kenken64/iot-door-sensor/docs/Annotation 2019-03-16 024516.png

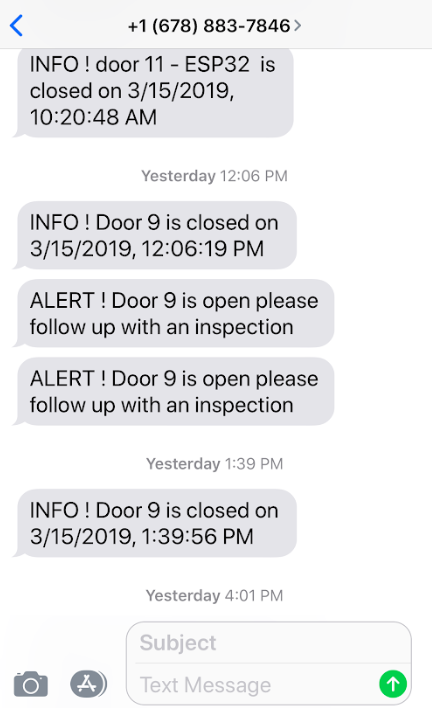
docs/Annotation 2019-03-16 024516.png
