kenken64/iot-door-sensor/docs/arduino_9.jpg

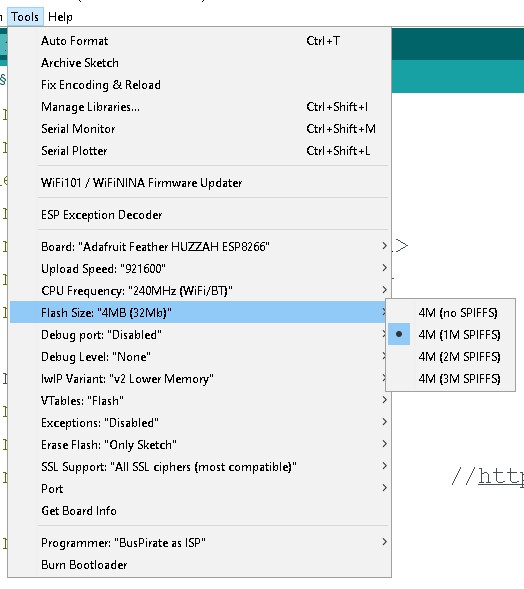
docs/arduino_9.jpg
