kenken64/iot-door-sensor/docs/blynk4.png

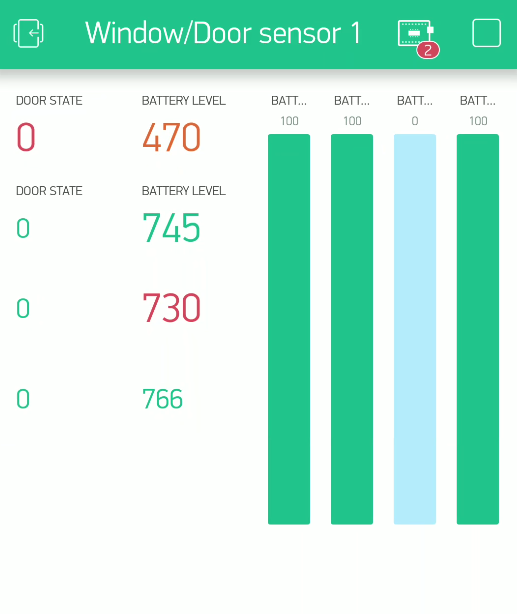
docs/blynk4.png
