kenken64/iot-door-sensor/docs/choose_date_action_was_taken.png

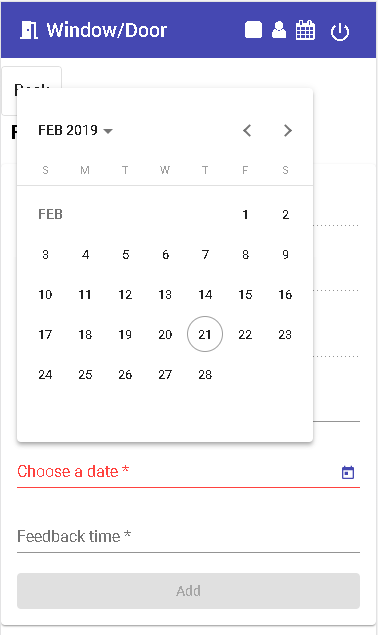
docs/choose_date_action_was_taken.png
