kenken64/iot-door-sensor/docs/door_sensor_wifi.jpg

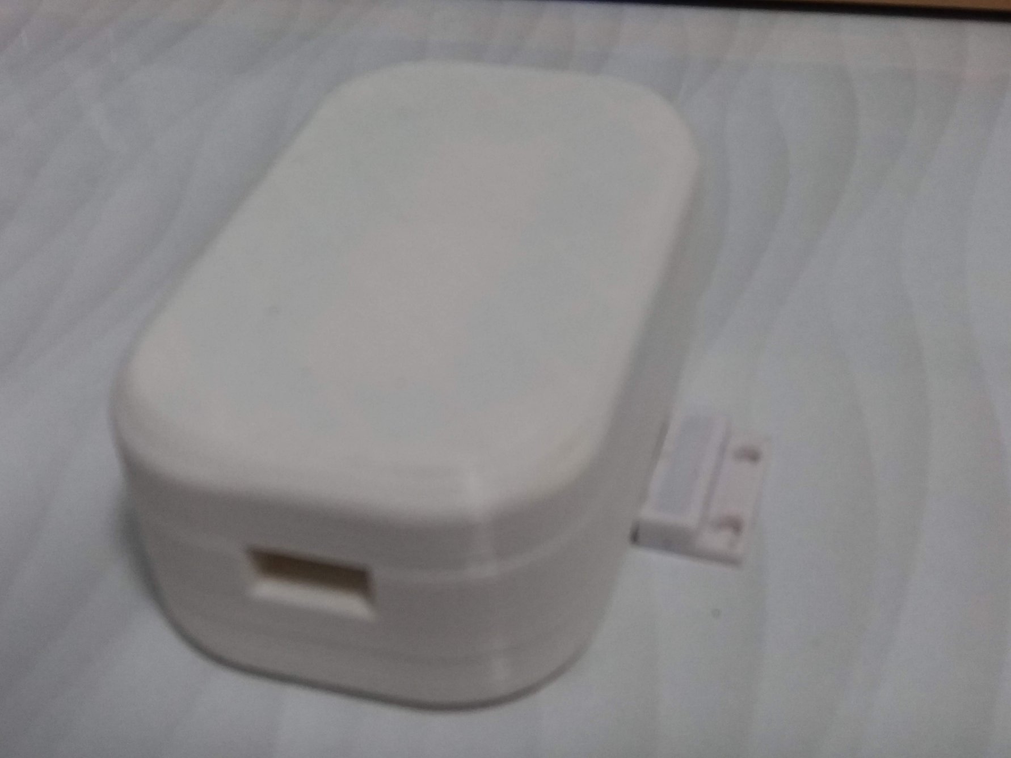
docs/door_sensor_wifi.jpg
