kenken64/iot-door-sensor/docs/filter_feedback.png

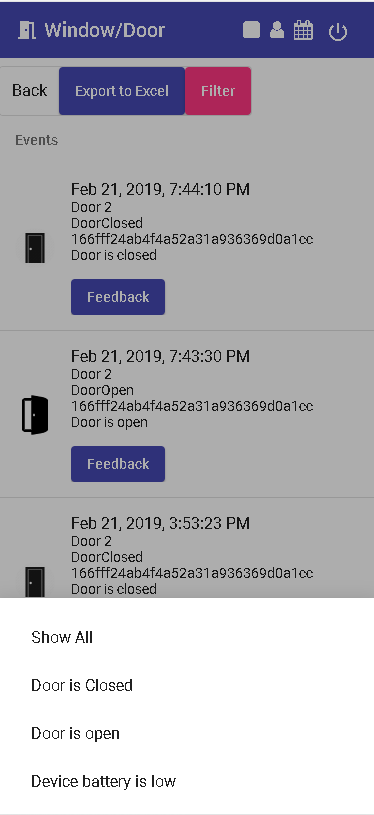
docs/filter_feedback.png
