kenken64/iot-door-sensor/docs/full_in_battery.png

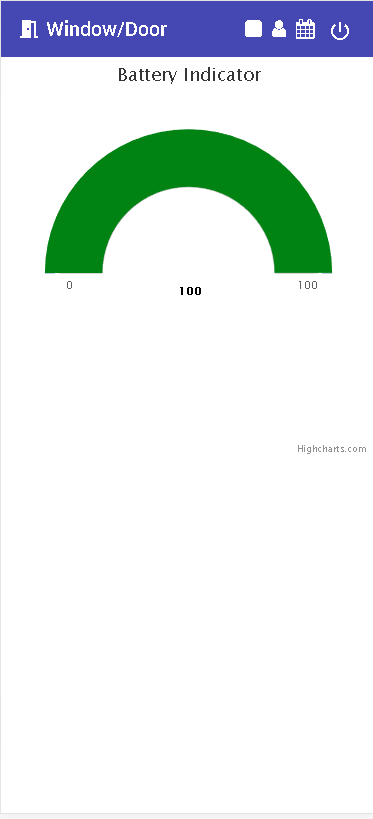
docs/full_in_battery.png
