kenken64/iot-door-sensor/docs/IMG_9706.PNG

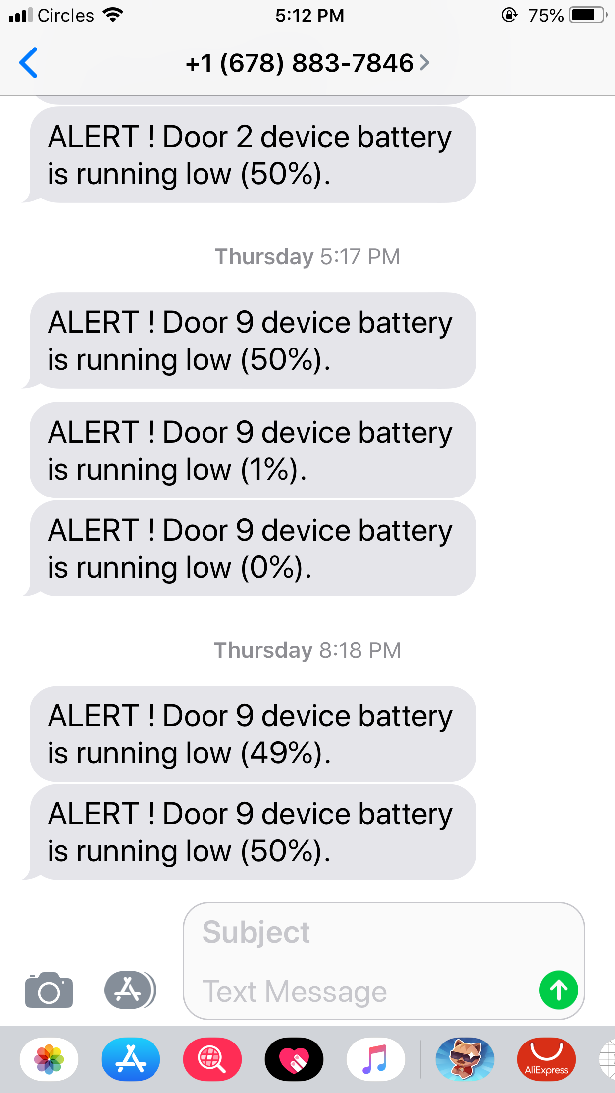
docs/IMG_9706.PNG
