kenken64/iot-door-sensor/docs/IMG_9707.PNG

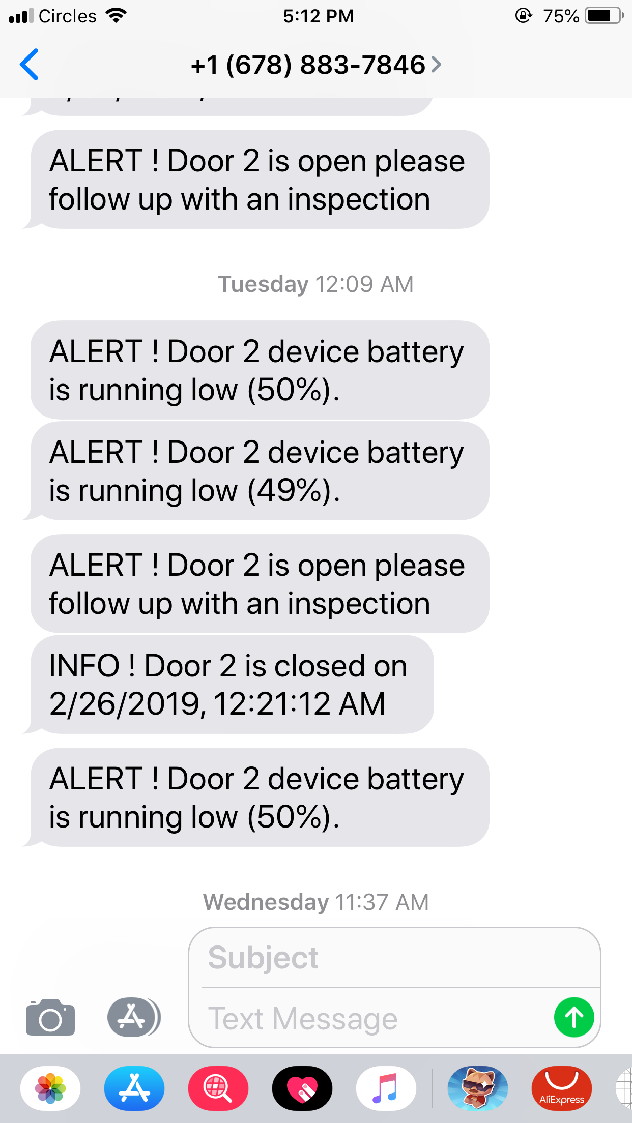
docs/IMG_9707.PNG
