kenken64/iot-door-sensor/docs/IMG_9709.PNG

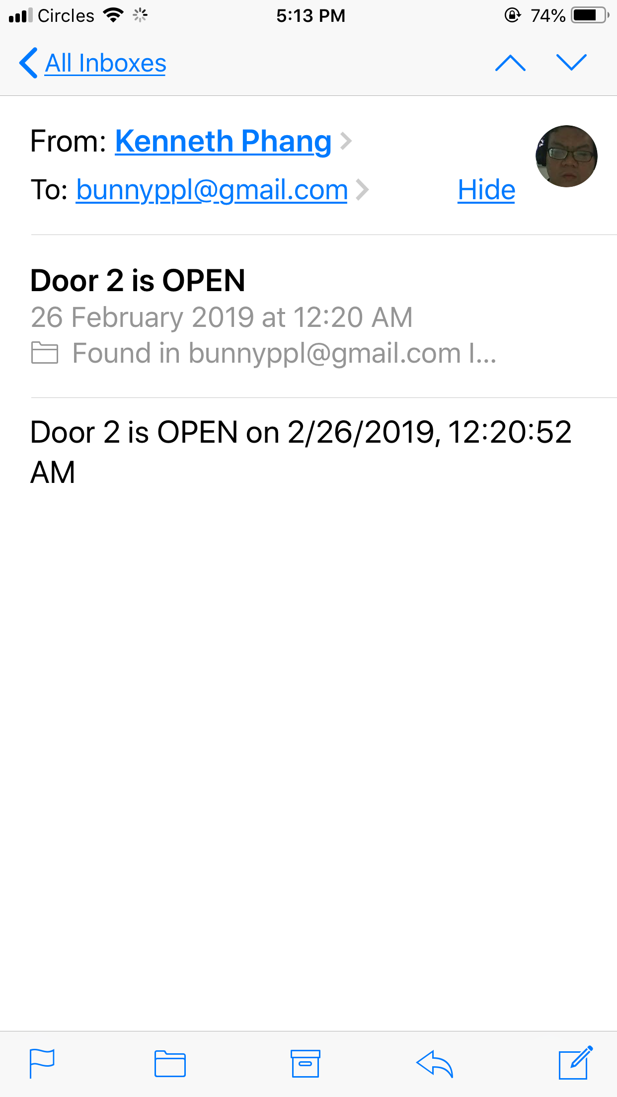
docs/IMG_9709.PNG
