kenken64/iot-door-sensor/docs/IMG_9710.PNG

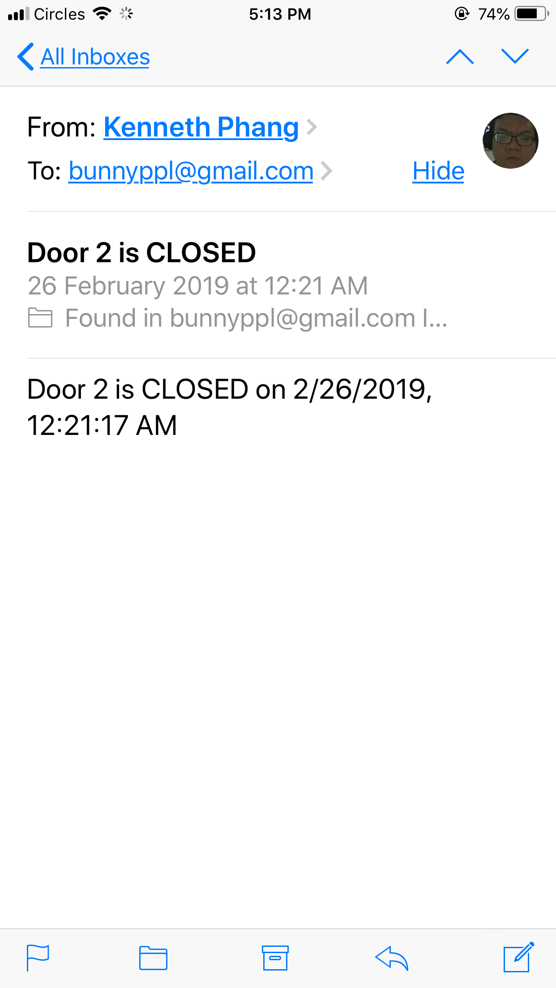
docs/IMG_9710.PNG
