kenken64/iot-door-sensor/docs/list_of_feedback.png

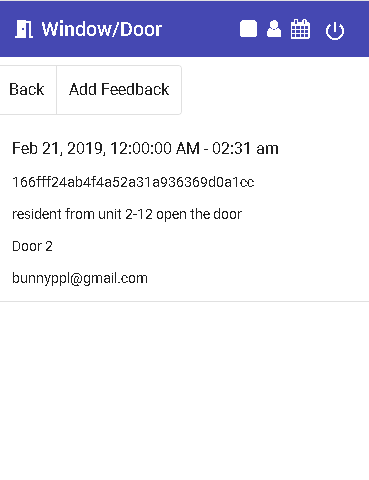
docs/list_of_feedback.png
