kenken64/iot-door-sensor/docs/listoffeedback_ondoor.jpg.png

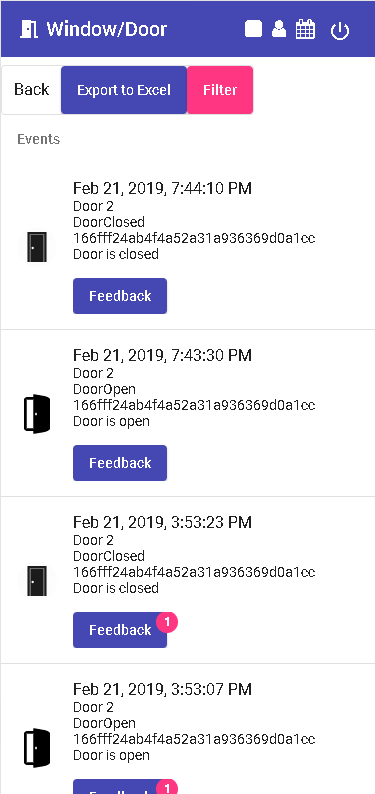
docs/listoffeedback_ondoor.jpg.png
