kenken64/iot-door-sensor/docs/out_of_battery.png

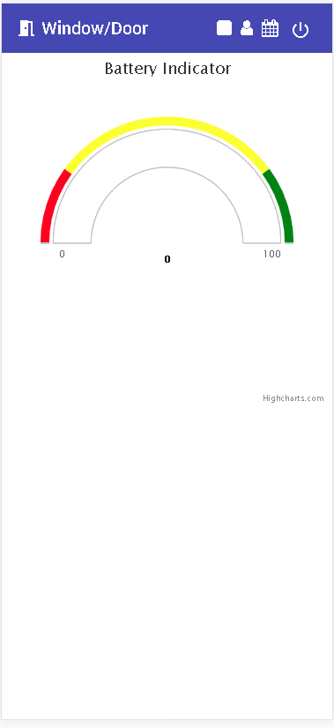
docs/out_of_battery.png
