kenken64/iot-door-sensor/docs/screenshot_1.png

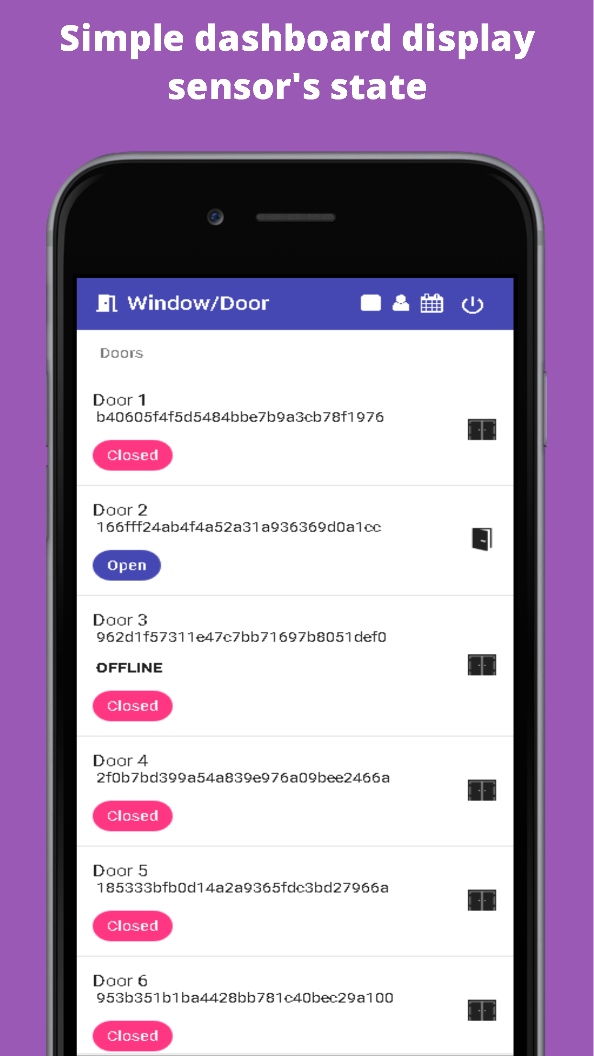
docs/screenshot_1.png
