kenken64/iot-door-sensor/docs/screenshot_2.png

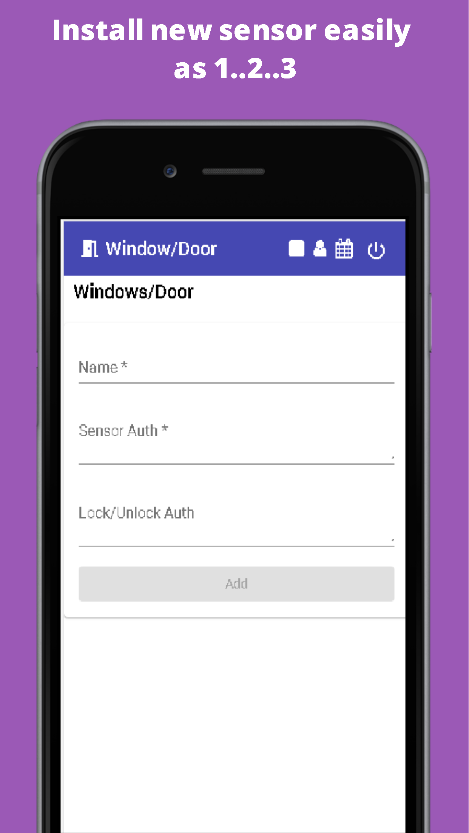
docs/screenshot_2.png
