kenken64/iot-door-sensor/docs/screenshot_3.png

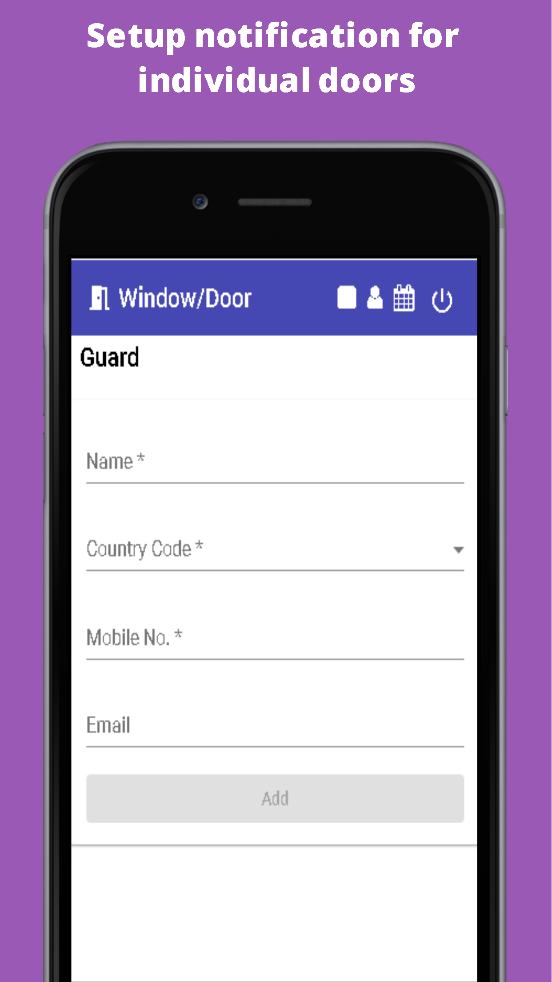
docs/screenshot_3.png
