kenken64/iot-door-sensor/docs/screenshot_4.png

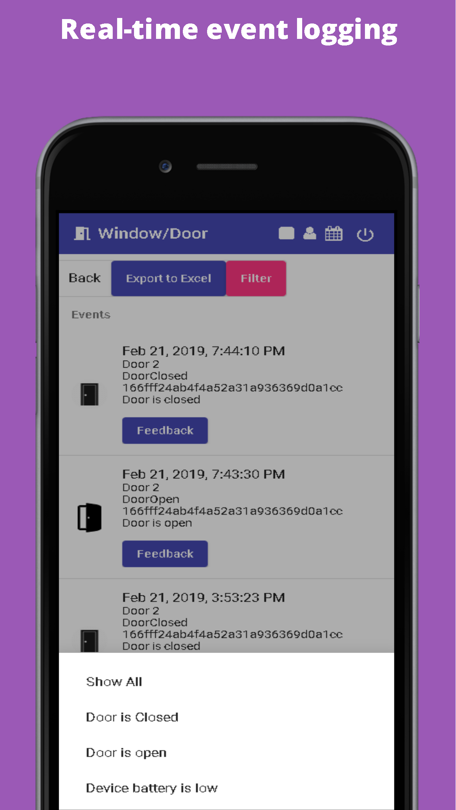
docs/screenshot_4.png
