kenken64/iot-door-sensor/docs/screenshot_5.png

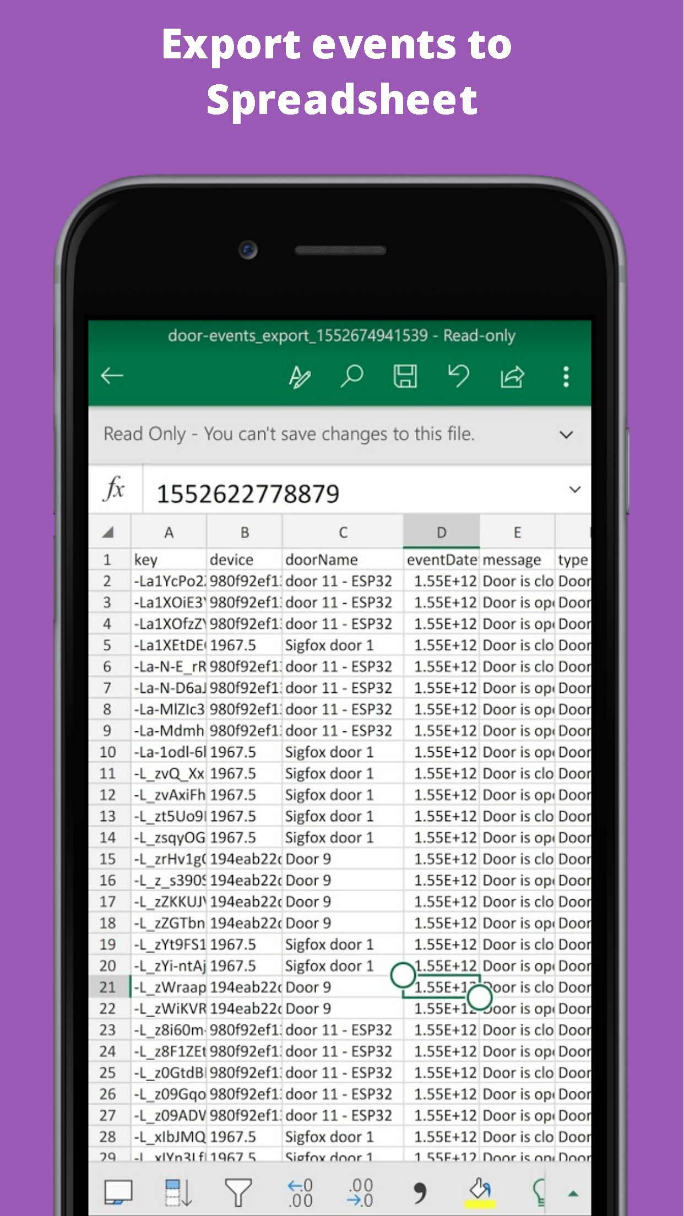
docs/screenshot_5.png
