kenken64/iot-door-sensor/docs/screenshot_6.png

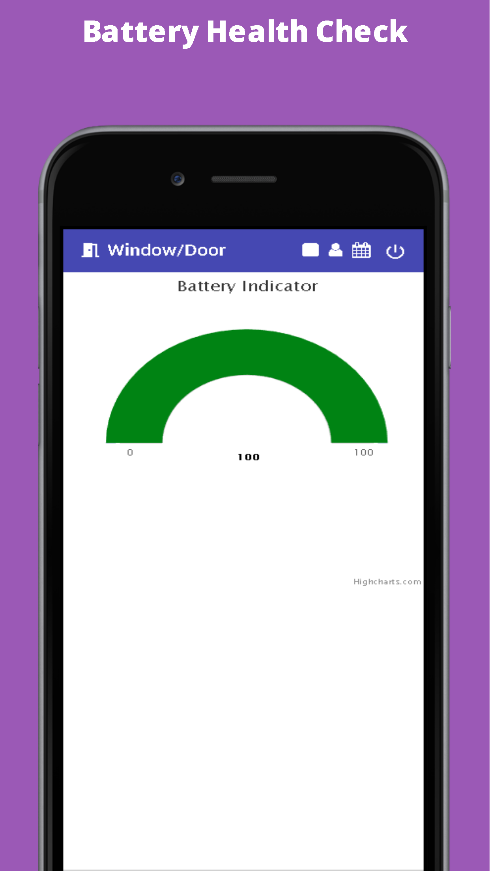
docs/screenshot_6.png
