kenken64/iot-door-sensor/docs/screenshot_9.png

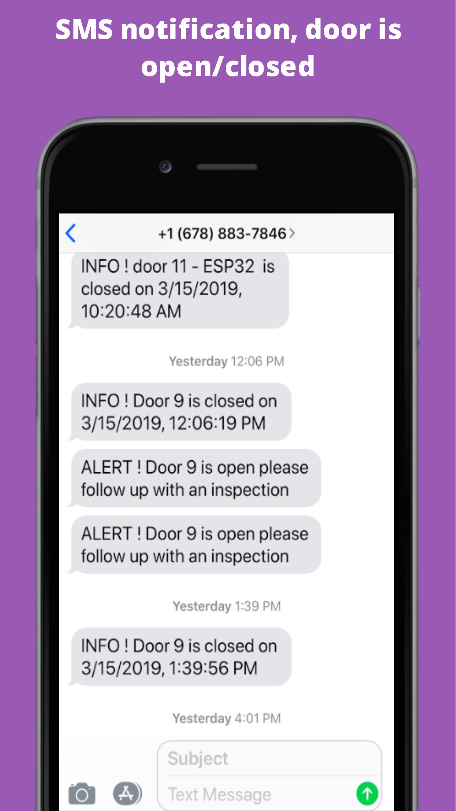
docs/screenshot_9.png
