kenken64/iot-door-sensor/docs/selected_guard_door.png

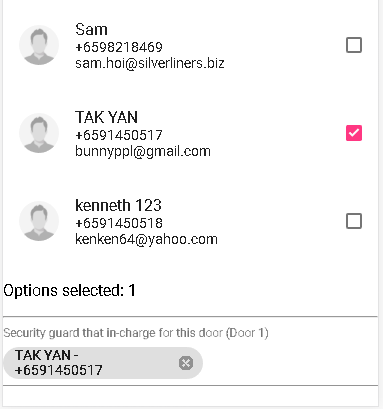
docs/selected_guard_door.png
