kenken64/iot-door-sensor/docs/sigfox_version1.jpg

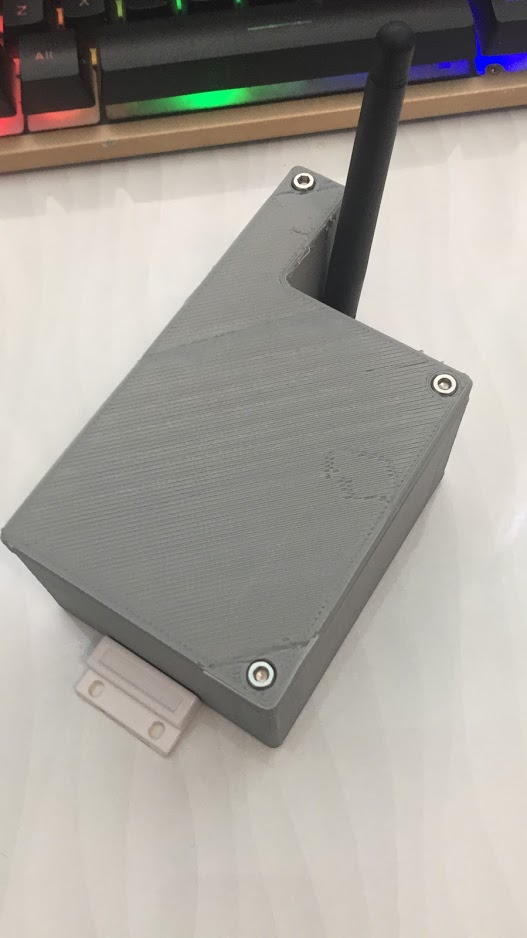
docs/sigfox_version1.jpg
