kenken64/iot-door-sensor/docs/tindie/configure_guard_door.jpg

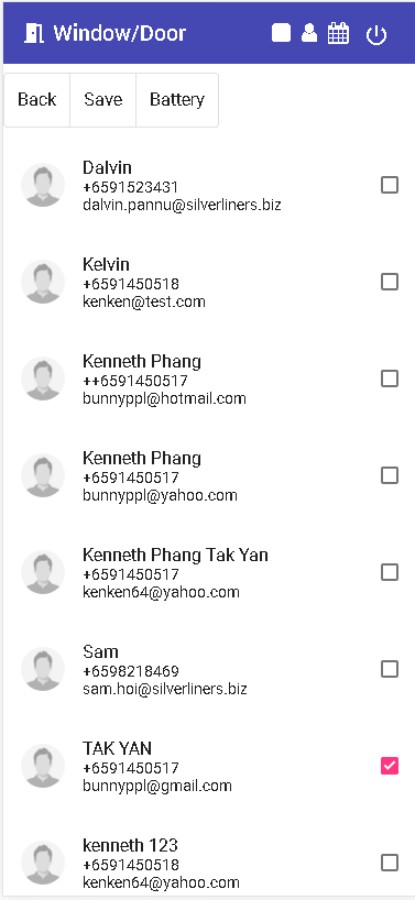
docs/tindie/configure_guard_door.jpg
