kenken64/iot-door-sensor/docs/tindie/list.jpg

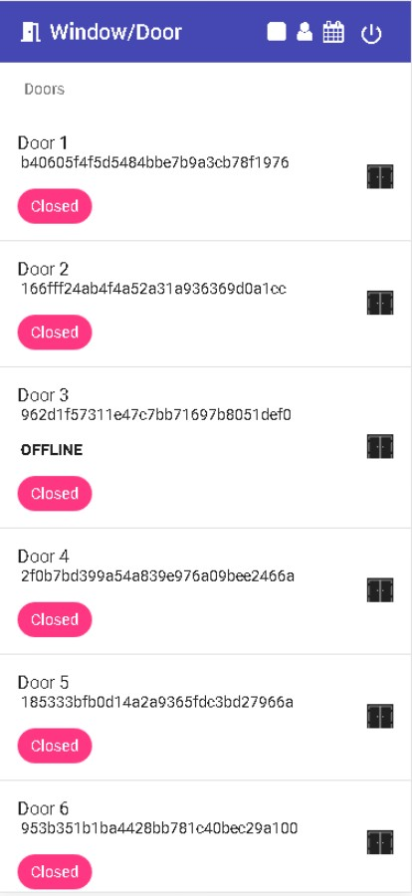
docs/tindie/list.jpg
