kenken64/iot-door-sensor/door-sensor_bb.png

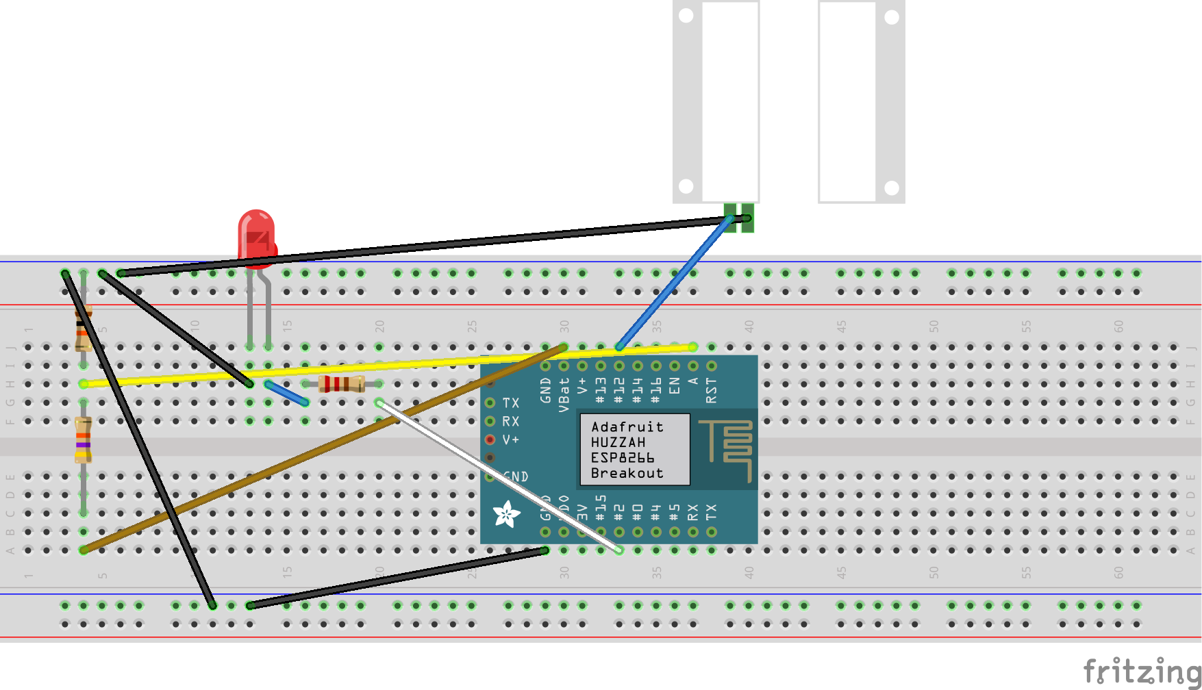
door-sensor_bb.png
